ElektorLabs/esp32-energymeter/images/IMG_0346.JPG

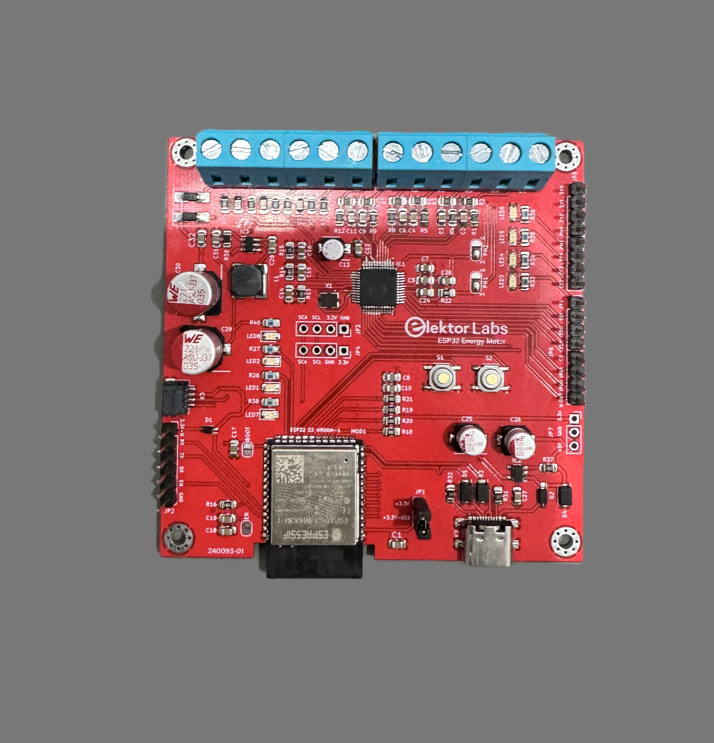
images/IMG_0346.JPG
