ElektorLabs/esp32-energymeter/images/IMG_0350.JPG

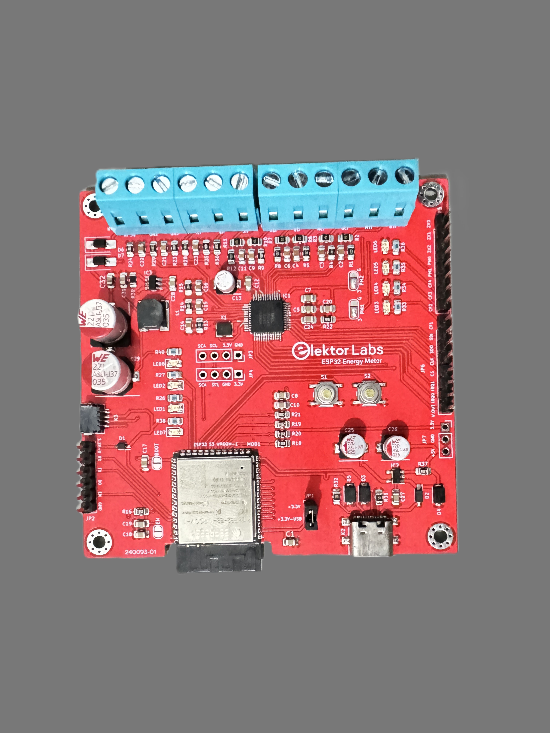
images/IMG_0350.JPG
