ElektorLabs/esp32-energymeter/images/IMG_0402.JPG

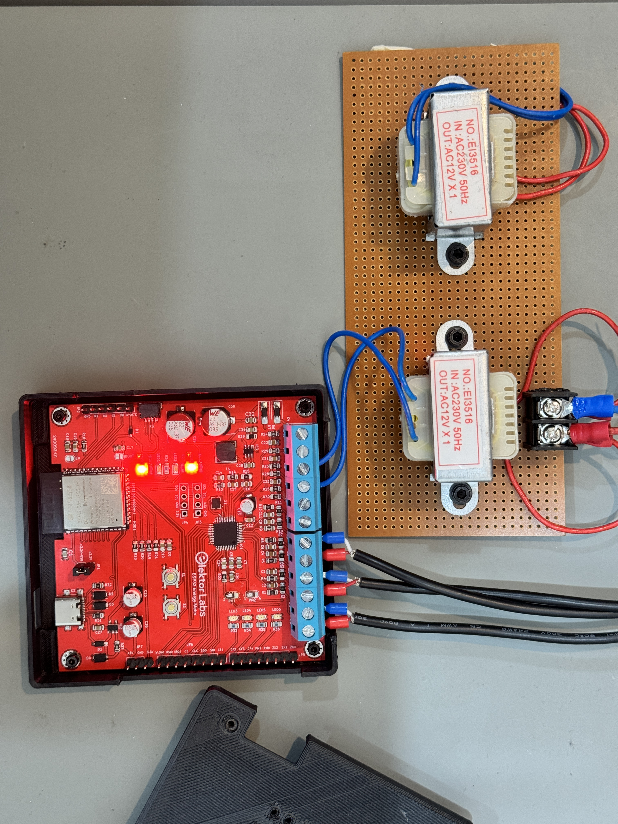
images/IMG_0402.JPG
